benkhant/NorthStar-Adaptation-Guide/LinkedListAR_Unity6/Assets/Markers/head_20.png

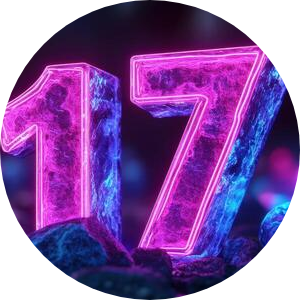
LinkedListAR_Unity6/Assets/Markers/head_20.png
