benkhant/NorthStar-Adaptation-Guide/LinkedListAR_Unity6/Assets/Markers/head_30.png

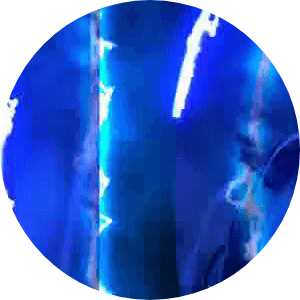
LinkedListAR_Unity6/Assets/Markers/head_30.png
