benkhant/NorthStar-Adaptation-Guide/LinkedListAR_Unity6/Assets/Markers/head_45.png

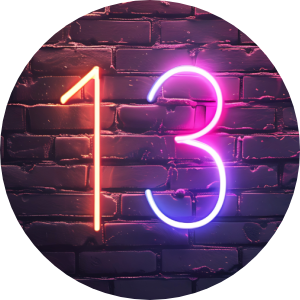
LinkedListAR_Unity6/Assets/Markers/head_45.png
