benkhant/NorthStar-Adaptation-Guide/LinkedListAR_Unity6/Assets/Markers/node_10.png

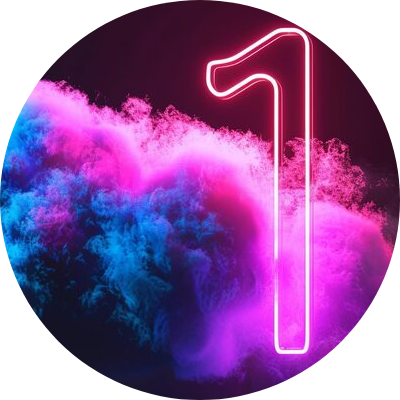
LinkedListAR_Unity6/Assets/Markers/node_10.png
