benkhant/NorthStar-Adaptation-Guide/LinkedListAR_Unity6/Assets/Markers/node_15.png

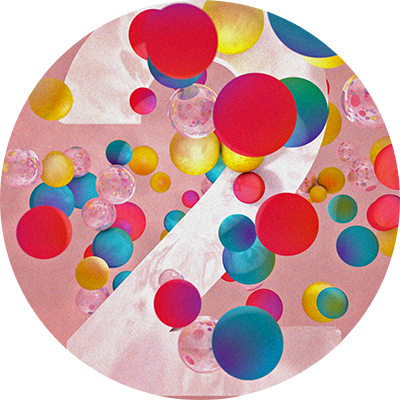
LinkedListAR_Unity6/Assets/Markers/node_15.png
