benkhant/NorthStar-Adaptation-Guide/LinkedListAR_Unity6/Assets/Markers/node_20.png

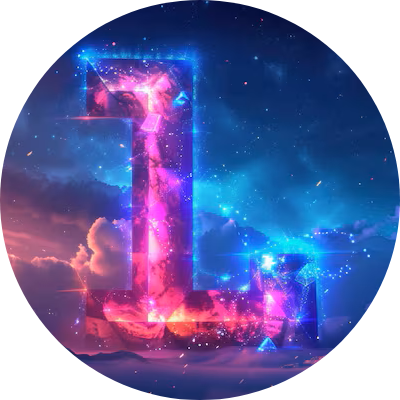
LinkedListAR_Unity6/Assets/Markers/node_20.png
