benkhant/NorthStar-Adaptation-Guide/LinkedListAR_Unity6/Assets/Markers/node_45.png

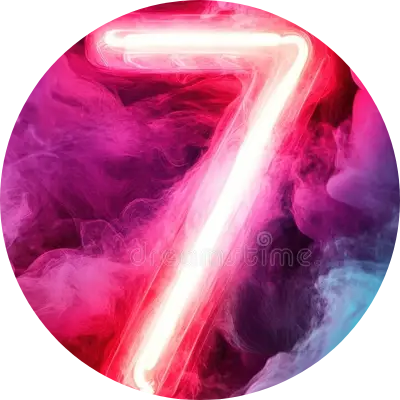
LinkedListAR_Unity6/Assets/Markers/node_45.png
