benkhant/NorthStar-Adaptation-Guide/LinkedListAR_Unity6/Assets/MRTK/Examples/Demos/EyeTracking/DemoScrollPanZoom/Textures/scrollbarhandle.png

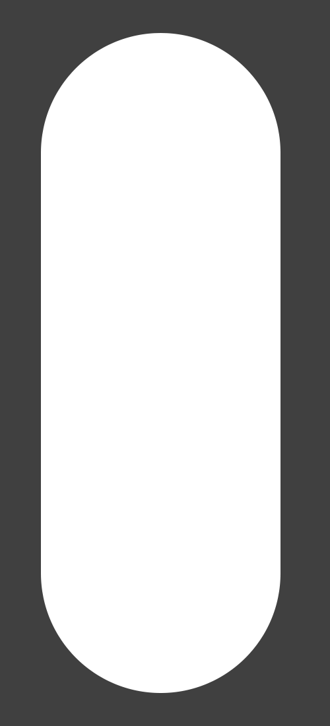
LinkedListAR_Unity6/Assets/MRTK/Examples/Demos/EyeTracking/DemoScrollPanZoom/Textures/scrollbarhandle.png
