benkhant/NorthStar-Adaptation-Guide/LinkedListAR_Unity6/Assets/MRTK/Examples/Demos/EyeTracking/DemoScrollPanZoom/Textures/tex_PanAndZoom_text.png

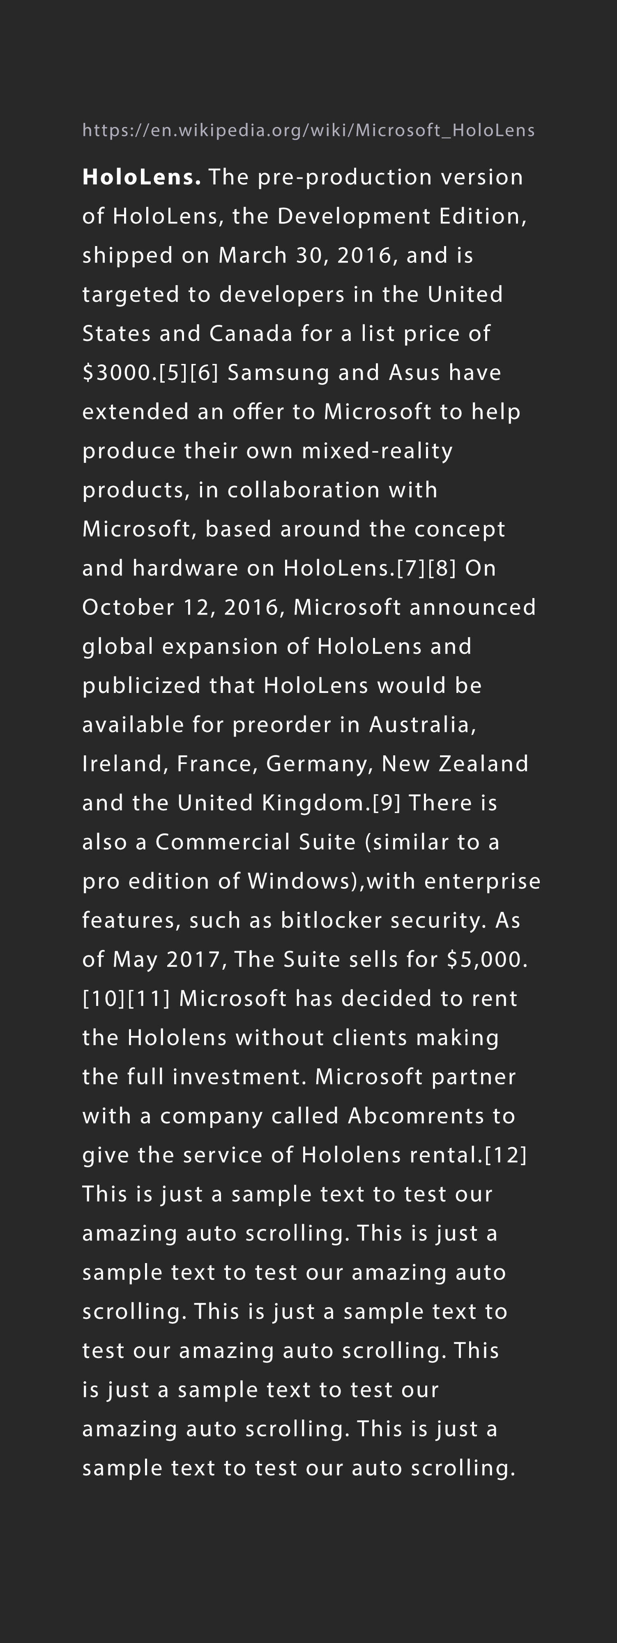
LinkedListAR_Unity6/Assets/MRTK/Examples/Demos/EyeTracking/DemoScrollPanZoom/Textures/tex_PanAndZoom_text.png
