benkhant/NorthStar-Adaptation-Guide/LinkedListAR_Unity6/Assets/MRTK/Examples/Demos/EyeTracking/DemoVisualizer/Textures/tex_picture2.jpg

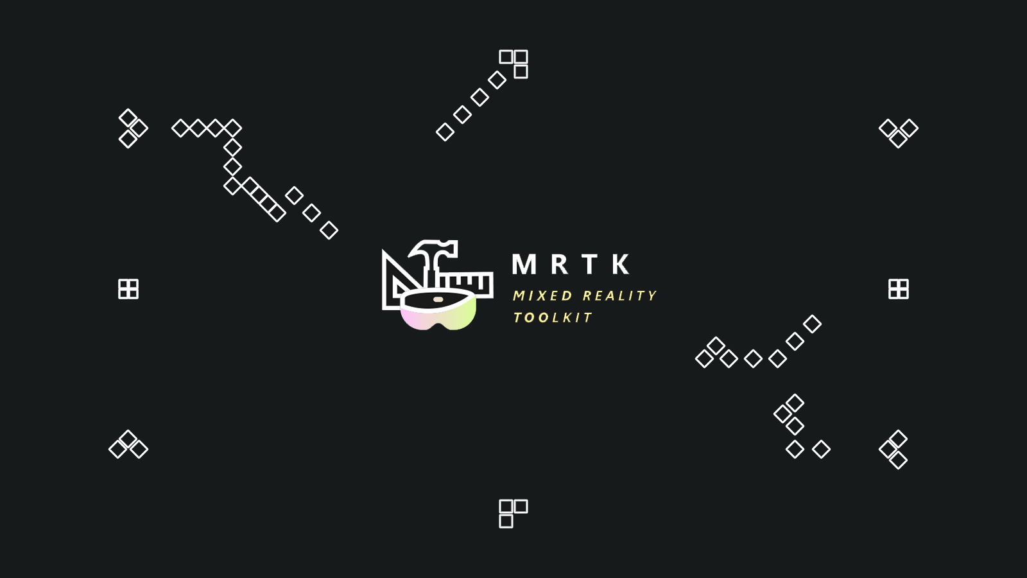
LinkedListAR_Unity6/Assets/MRTK/Examples/Demos/EyeTracking/DemoVisualizer/Textures/tex_picture2.jpg
