benkhant/NorthStar-Adaptation-Guide/LinkedListAR_Unity6/Assets/MRTK/Examples/Demos/EyeTracking/General/Textures/tex_blank_tile.png

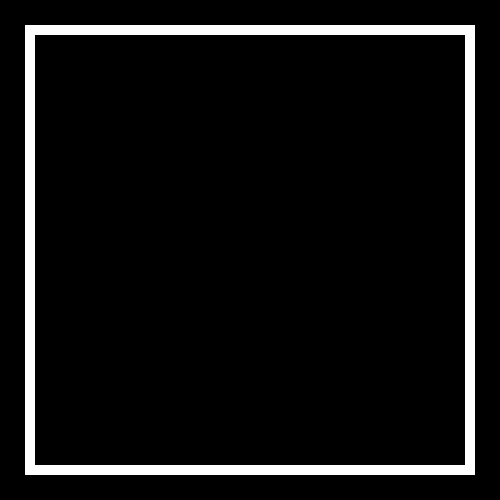
LinkedListAR_Unity6/Assets/MRTK/Examples/Demos/EyeTracking/General/Textures/tex_blank_tile.png
