benkhant/NorthStar-Adaptation-Guide/LinkedListAR_Unity6/Assets/MRTK/Examples/Demos/Gltf/Models/Avocado/glTF/Avocado_baseColor.png

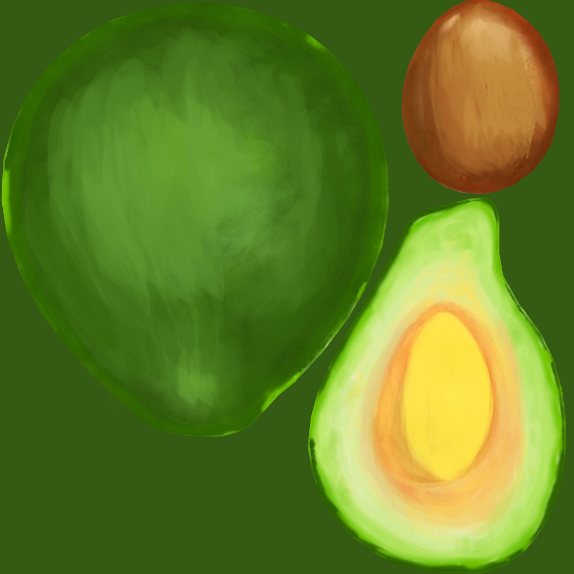
LinkedListAR_Unity6/Assets/MRTK/Examples/Demos/Gltf/Models/Avocado/glTF/Avocado_baseColor.png
