benkhant/NorthStar-Adaptation-Guide/LinkedListAR_Unity6/Assets/MRTK/Examples/Demos/UX/Interactables/Textures/PhysicalTouch.png

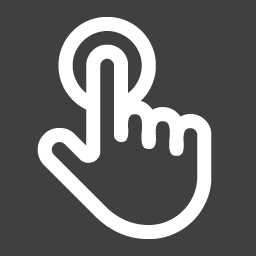
LinkedListAR_Unity6/Assets/MRTK/Examples/Demos/UX/Interactables/Textures/PhysicalTouch.png
