benkhant/NorthStar-Adaptation-Guide/LinkedListAR_Unity6/Assets/MRTK/Examples/StandardAssets/Models/CoffeeCup 1.fbm/5.png

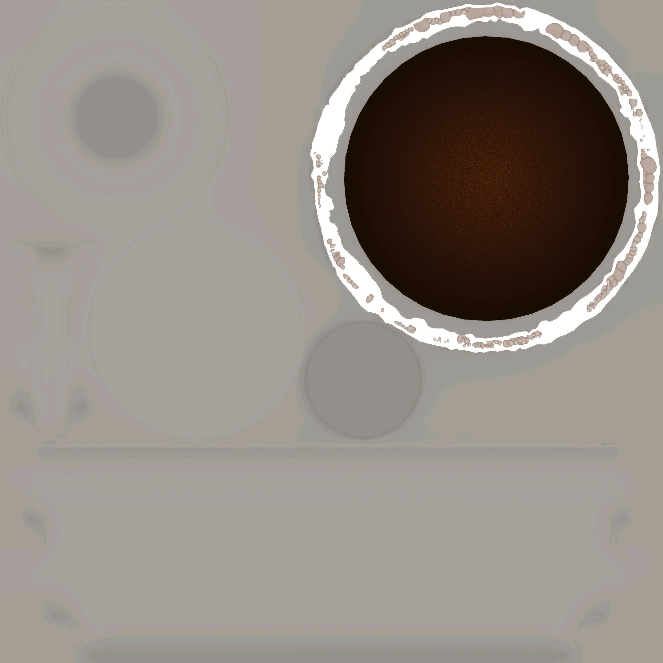
LinkedListAR_Unity6/Assets/MRTK/Examples/StandardAssets/Models/CoffeeCup 1.fbm/5.png
