benkhant/NorthStar-Adaptation-Guide/LinkedListAR_Unity6/Assets/MRTK/Examples/StandardAssets/Models/EarthCore.fbm/7.png

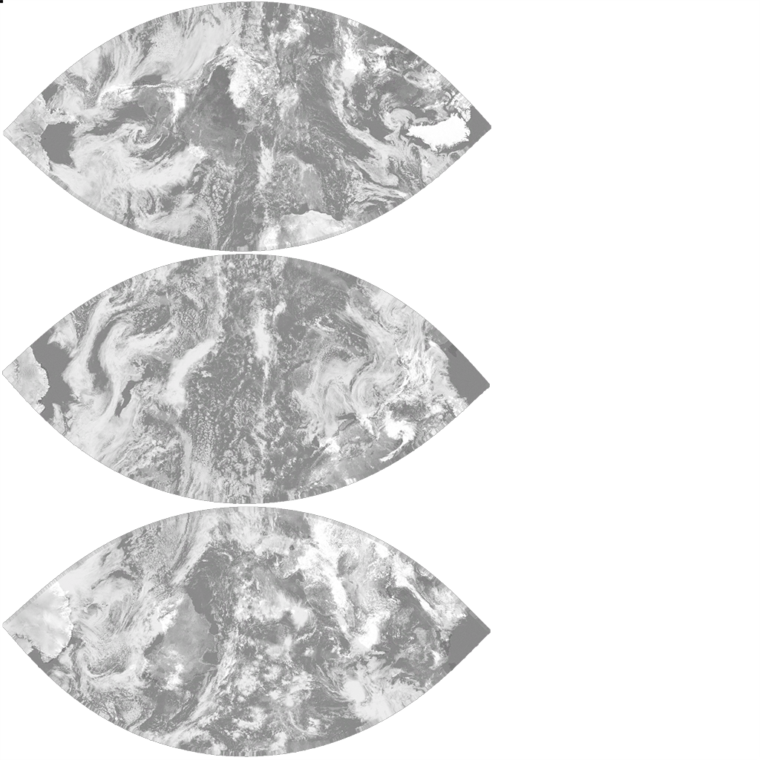
LinkedListAR_Unity6/Assets/MRTK/Examples/StandardAssets/Models/EarthCore.fbm/7.png
