benkhant/NorthStar-Adaptation-Guide/LinkedListAR_Unity6/Assets/MRTK/Examples/StandardAssets/Models/MarsCuriosityRover.fbm/6.png

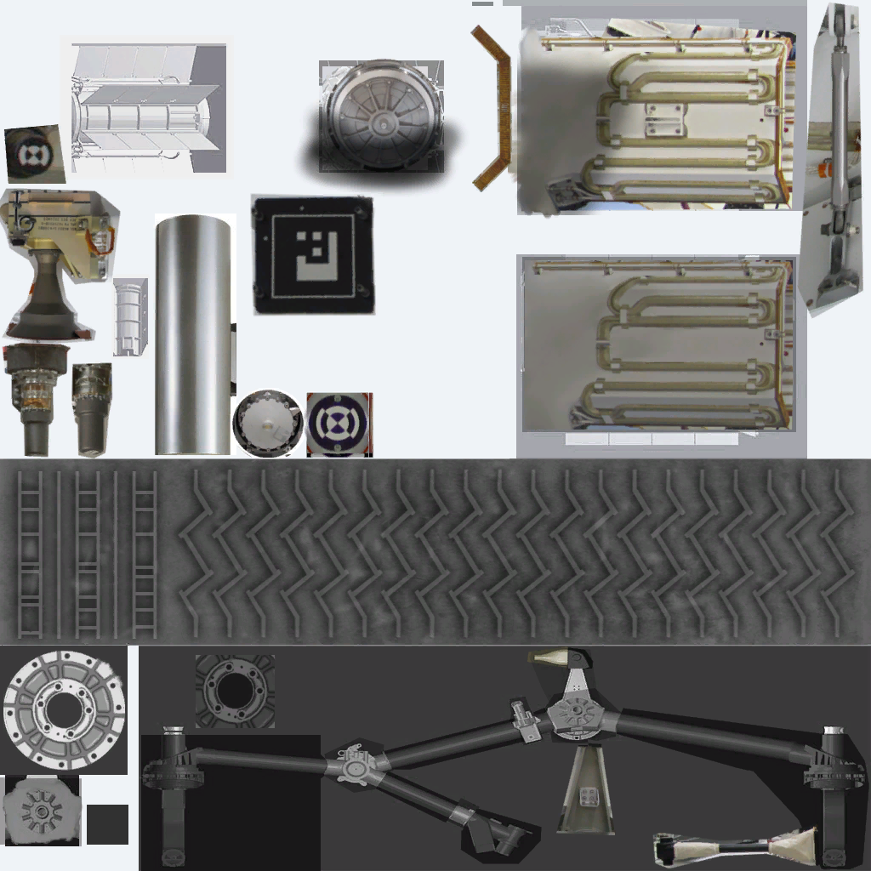
LinkedListAR_Unity6/Assets/MRTK/Examples/StandardAssets/Models/MarsCuriosityRover.fbm/6.png
