benkhant/NorthStar-Adaptation-Guide/LinkedListAR_Unity6/Assets/MRTK/Examples/StandardAssets/Models/MarsCuriosityRover.fbm/9.png

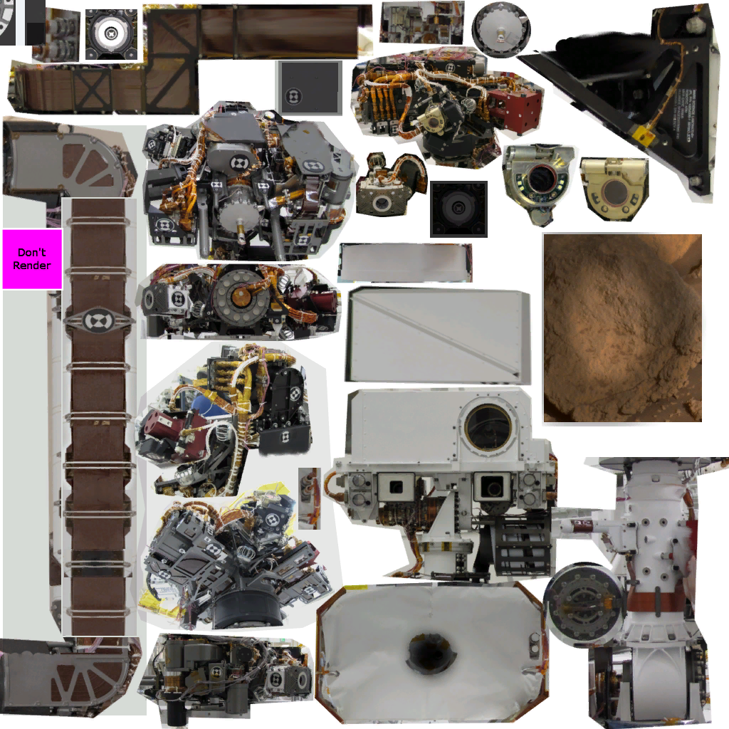
LinkedListAR_Unity6/Assets/MRTK/Examples/StandardAssets/Models/MarsCuriosityRover.fbm/9.png
