benkhant/NorthStar-Adaptation-Guide/LinkedListAR_Unity6/Assets/MRTK/Examples/StandardAssets/Textures/CoffeeFoam.png

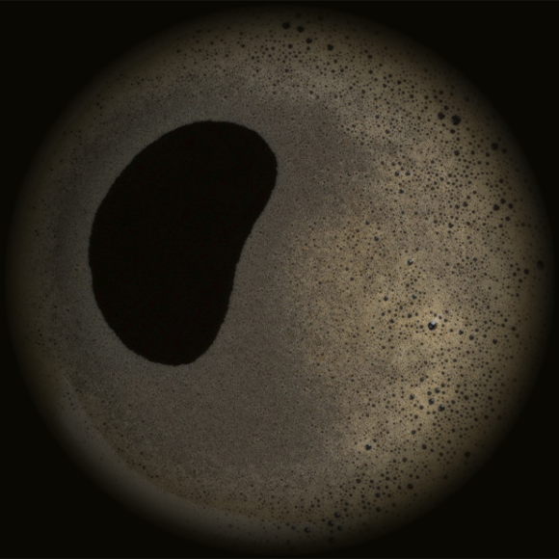
LinkedListAR_Unity6/Assets/MRTK/Examples/StandardAssets/Textures/CoffeeFoam.png
