benkhant/NorthStar-Adaptation-Guide/LinkedListAR_Unity6/Assets/MRTK/Examples/StandardAssets/Textures/Fabric_normal.png

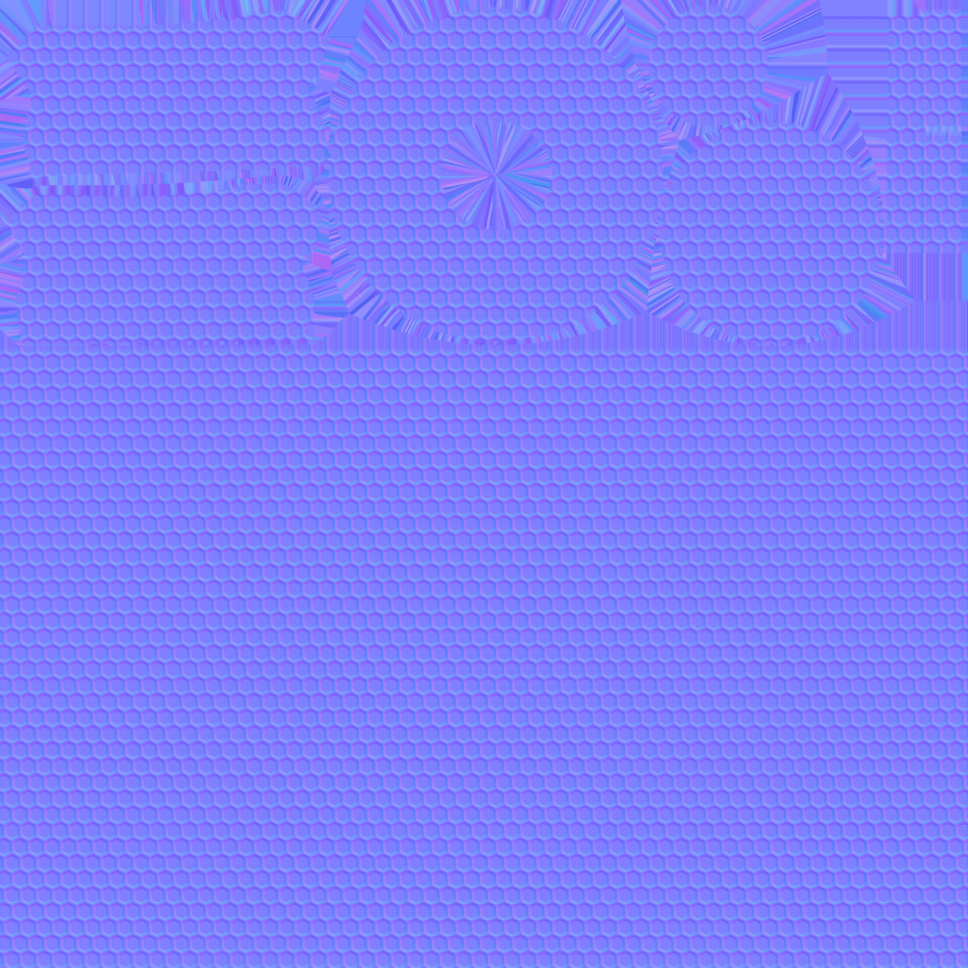
LinkedListAR_Unity6/Assets/MRTK/Examples/StandardAssets/Textures/Fabric_normal.png
