benkhant/NorthStar-Adaptation-Guide/LinkedListAR_Unity6/Assets/MRTK/Examples/StandardAssets/Textures/HumanHeart_Albdeo.png

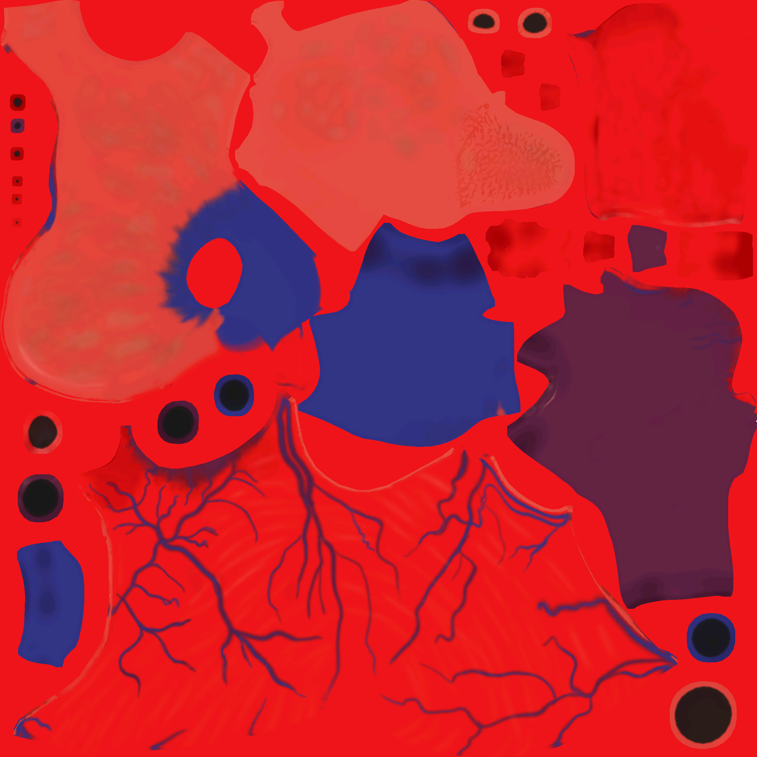
LinkedListAR_Unity6/Assets/MRTK/Examples/StandardAssets/Textures/HumanHeart_Albdeo.png
