benkhant/NorthStar-Adaptation-Guide/LinkedListAR_Unity6/Assets/MRTK/Examples/StandardAssets/Textures/PianoKeys_DIF.png

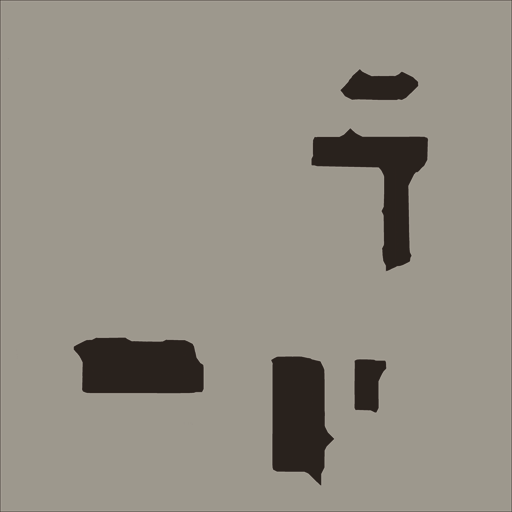
LinkedListAR_Unity6/Assets/MRTK/Examples/StandardAssets/Textures/PianoKeys_DIF.png
