benkhant/NorthStar-Adaptation-Guide/LinkedListAR_Unity6/Assets/MRTK/Examples/StandardAssets/Textures/PianoKeys_NM.png

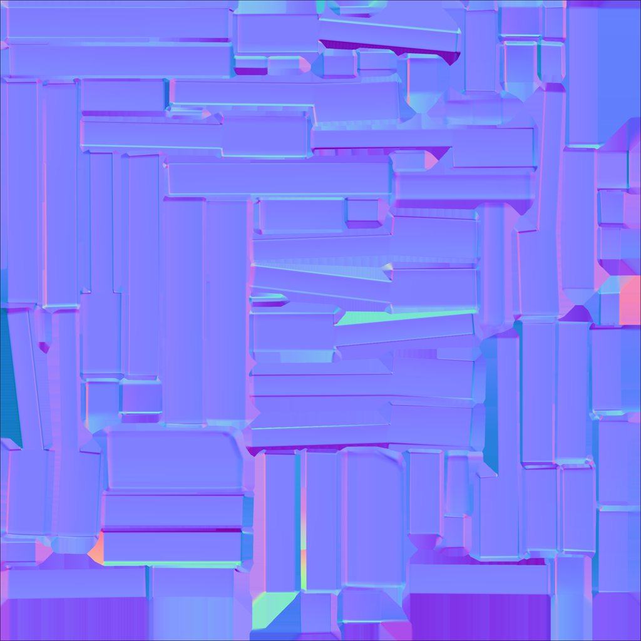
LinkedListAR_Unity6/Assets/MRTK/Examples/StandardAssets/Textures/PianoKeys_NM.png
