benkhant/NorthStar-Adaptation-Guide/LinkedListAR_Unity6/Assets/MRTK/Examples/StandardAssets/Textures/RustedIron_albedo.png

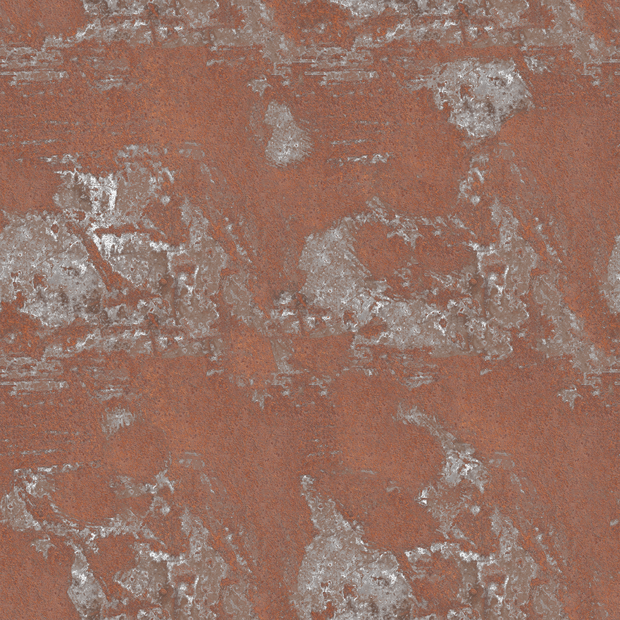
LinkedListAR_Unity6/Assets/MRTK/Examples/StandardAssets/Textures/RustedIron_albedo.png
