benkhant/NorthStar-Adaptation-Guide/LinkedListAR_Unity6/Assets/MRTK/Examples/StandardAssets/Textures/ShaderBall_albedo.png

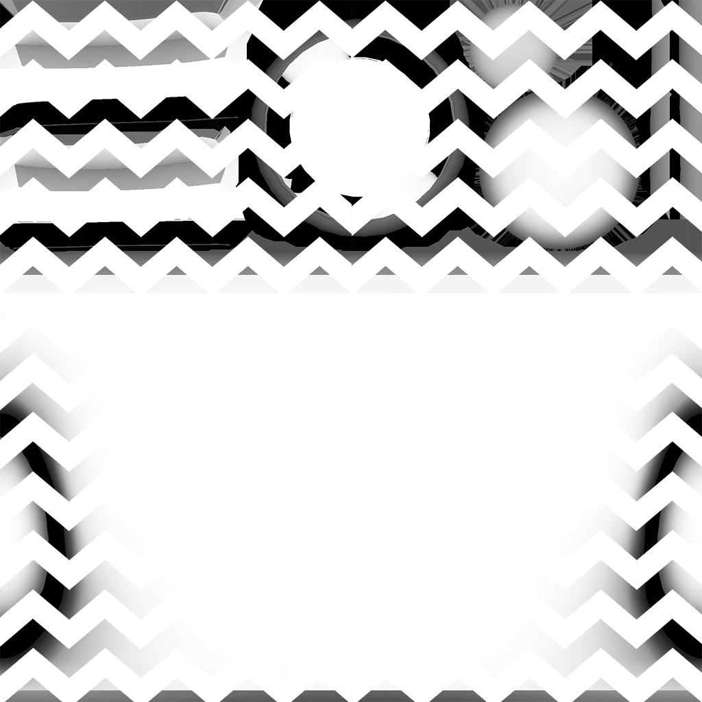
LinkedListAR_Unity6/Assets/MRTK/Examples/StandardAssets/Textures/ShaderBall_albedo.png
