benkhant/NorthStar-Adaptation-Guide/LinkedListAR_Unity6/Assets/MRTK/Examples/StandardAssets/Textures/ShaderBall_ao.png

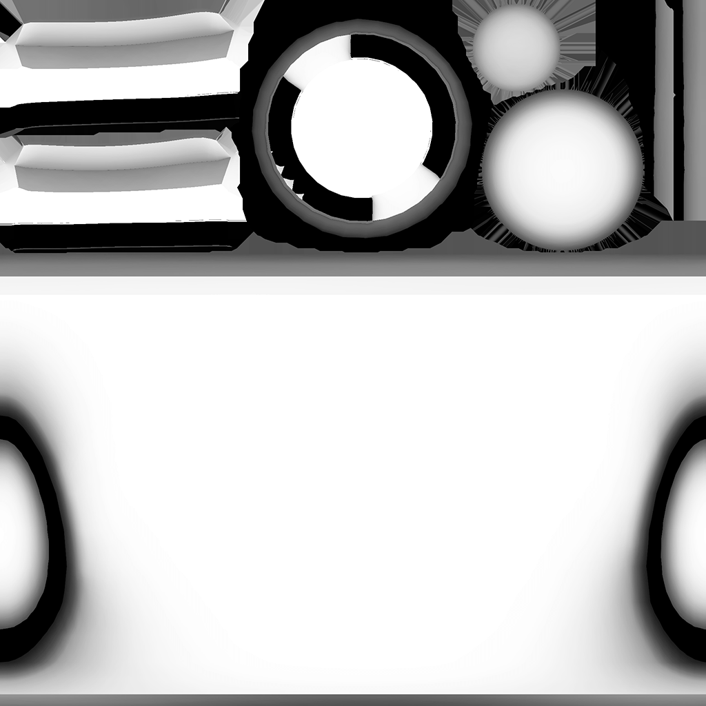
LinkedListAR_Unity6/Assets/MRTK/Examples/StandardAssets/Textures/ShaderBall_ao.png
