benkhant/NorthStar-Adaptation-Guide/LinkedListAR_Unity6/Assets/MRTK/Examples/StandardAssets/Textures/ShaderBallNoise_albedo.png

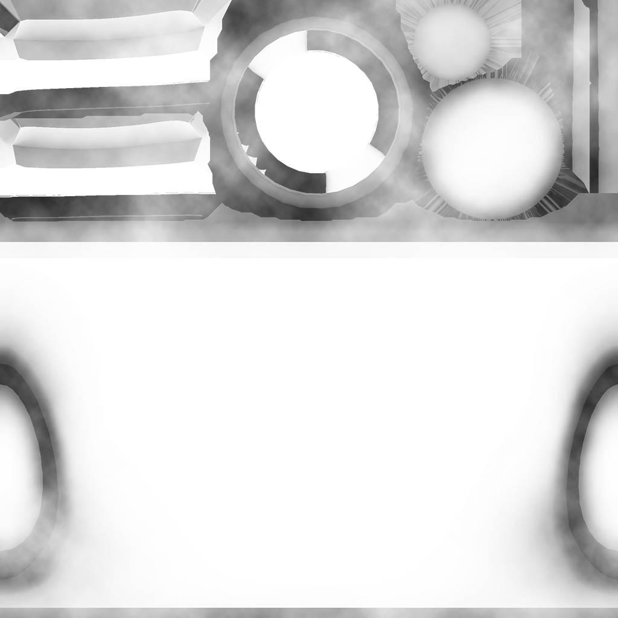
LinkedListAR_Unity6/Assets/MRTK/Examples/StandardAssets/Textures/ShaderBallNoise_albedo.png
