benkhant/NorthStar-Adaptation-Guide/LinkedListAR_Unity6/Assets/MRTK/Extensions/LostTrackingService/Assets/color_palette.png

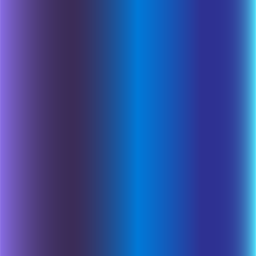
LinkedListAR_Unity6/Assets/MRTK/Extensions/LostTrackingService/Assets/color_palette.png
