benkhant/NorthStar-Adaptation-Guide/LinkedListAR_Unity6/Assets/MRTK/SDK/StandardAssets/Textures/Checker_albedo.png

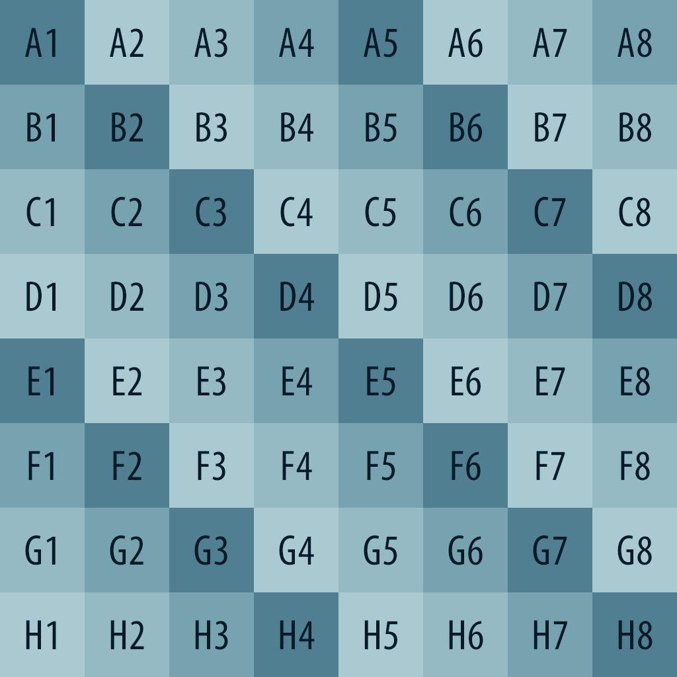
LinkedListAR_Unity6/Assets/MRTK/SDK/StandardAssets/Textures/Checker_albedo.png
