benkhant/NorthStar-Adaptation-Guide/LinkedListAR_Unity6/Assets/MRTK/SDK/StandardAssets/Textures/Circle.png

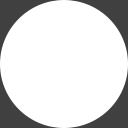
LinkedListAR_Unity6/Assets/MRTK/SDK/StandardAssets/Textures/Circle.png
