benkhant/NorthStar-Adaptation-Guide/LinkedListAR_Unity6/Assets/MRTK/SDK/StandardAssets/Textures/GrabArea.png

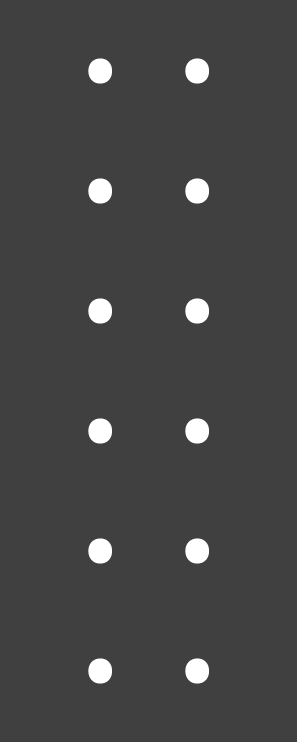
LinkedListAR_Unity6/Assets/MRTK/SDK/StandardAssets/Textures/GrabArea.png
