benkhant/NorthStar-Adaptation-Guide/LinkedListAR_Unity6/Assets/MRTK/SDK/StandardAssets/Textures/PanExampleContent.jpg

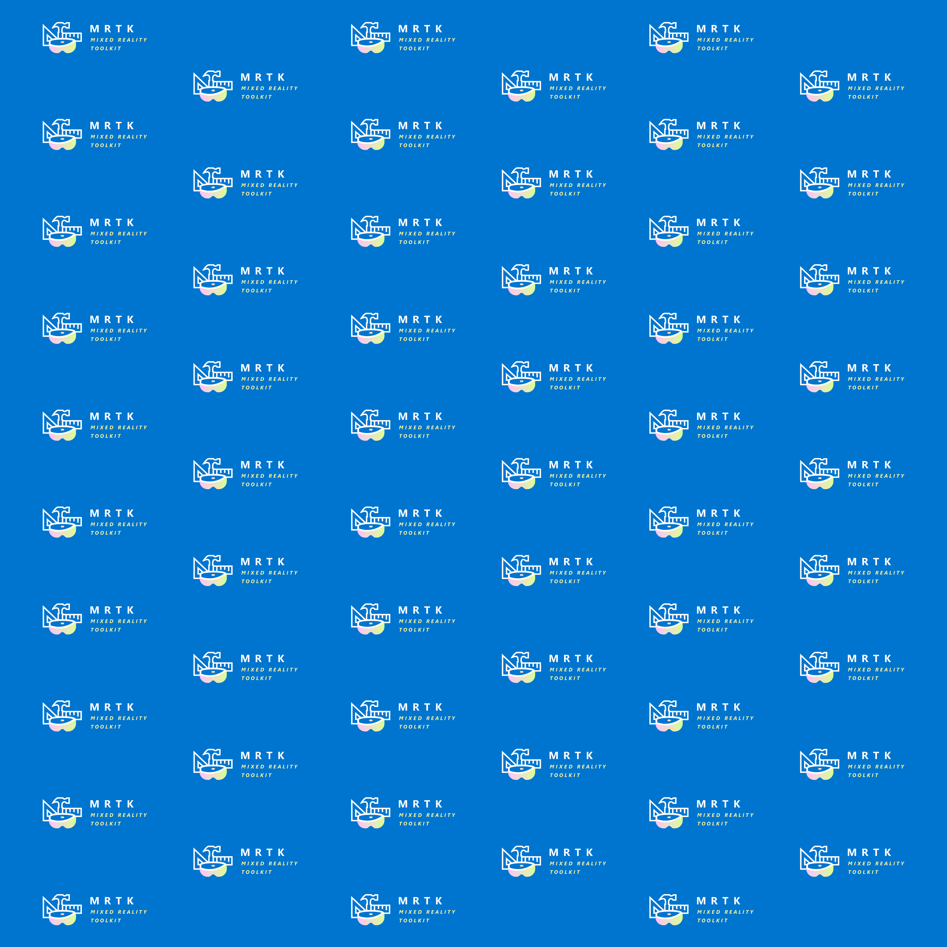
LinkedListAR_Unity6/Assets/MRTK/SDK/StandardAssets/Textures/PanExampleContent.jpg
