benkhant/NorthStar-Adaptation-Guide/LinkedListAR_Unity6/Assets/MRTK/SDK/StandardAssets/Textures/ResetRotation.png

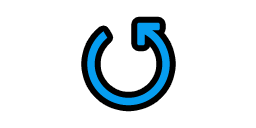
LinkedListAR_Unity6/Assets/MRTK/SDK/StandardAssets/Textures/ResetRotation.png
