benkhant/NorthStar-Adaptation-Guide/LinkedListAR_Unity6/Assets/MRTK/StandardAssets/Textures/Generic_controller_black_scaled.png

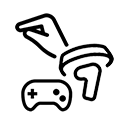
LinkedListAR_Unity6/Assets/MRTK/StandardAssets/Textures/Generic_controller_black_scaled.png
