benkhant/NorthStar-Adaptation-Guide/LinkedListAR_Unity6/Assets/MRTK/StandardAssets/Textures/Generic_controller_white_scaled.png

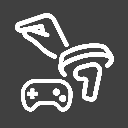
LinkedListAR_Unity6/Assets/MRTK/StandardAssets/Textures/Generic_controller_white_scaled.png
