benkhant/NorthStar-Adaptation-Guide/LinkedListAR_Unity6/Assets/MRTK/StandardAssets/Textures/IridescentSpectrum.png

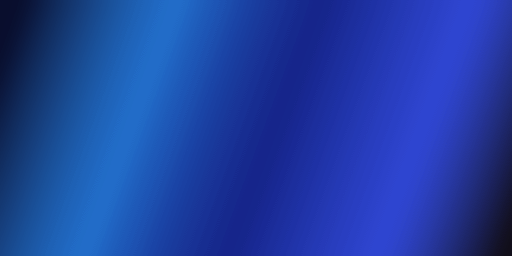
LinkedListAR_Unity6/Assets/MRTK/StandardAssets/Textures/IridescentSpectrum.png
