benkhant/NorthStar-Adaptation-Guide/LinkedListAR_Unity6/Assets/MRTK/StandardAssets/Textures/MotionController_left_black.png

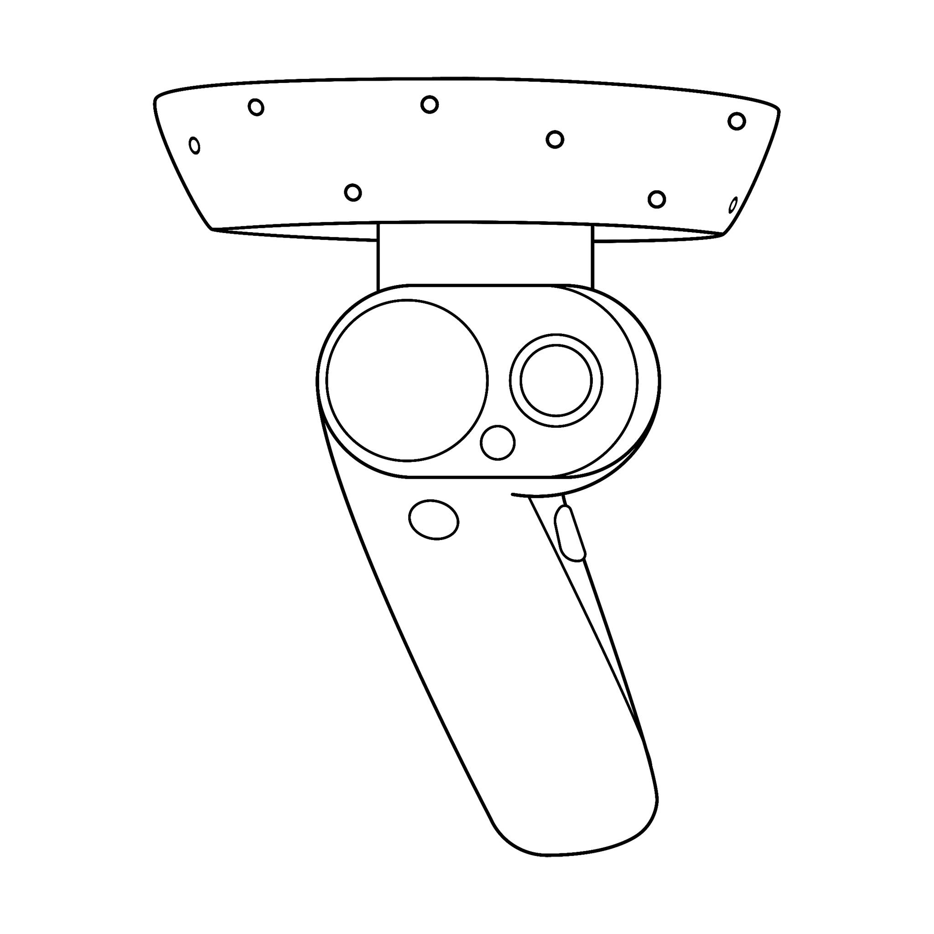
LinkedListAR_Unity6/Assets/MRTK/StandardAssets/Textures/MotionController_left_black.png
