benkhant/NorthStar-Adaptation-Guide/LinkedListAR_Unity6/Assets/MRTK/StandardAssets/Textures/OculusControllersTouch_left_white.png

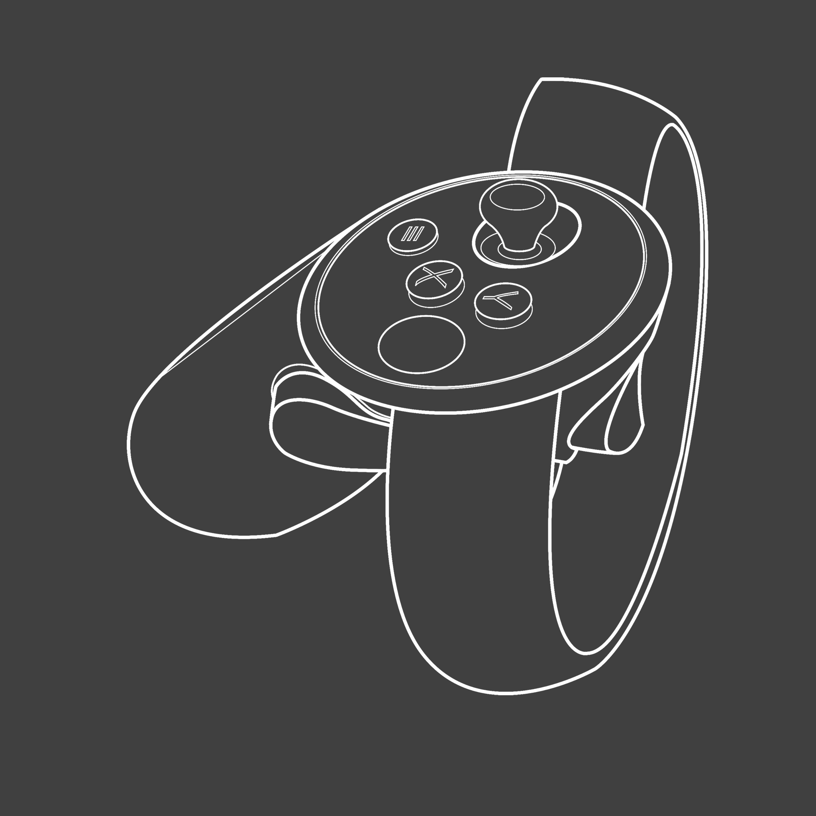
LinkedListAR_Unity6/Assets/MRTK/StandardAssets/Textures/OculusControllersTouch_left_white.png
