benkhant/NorthStar-Adaptation-Guide/LinkedListAR_Unity6/Assets/MRTK/StandardAssets/Textures/OculusControllersTouch_right_white.png

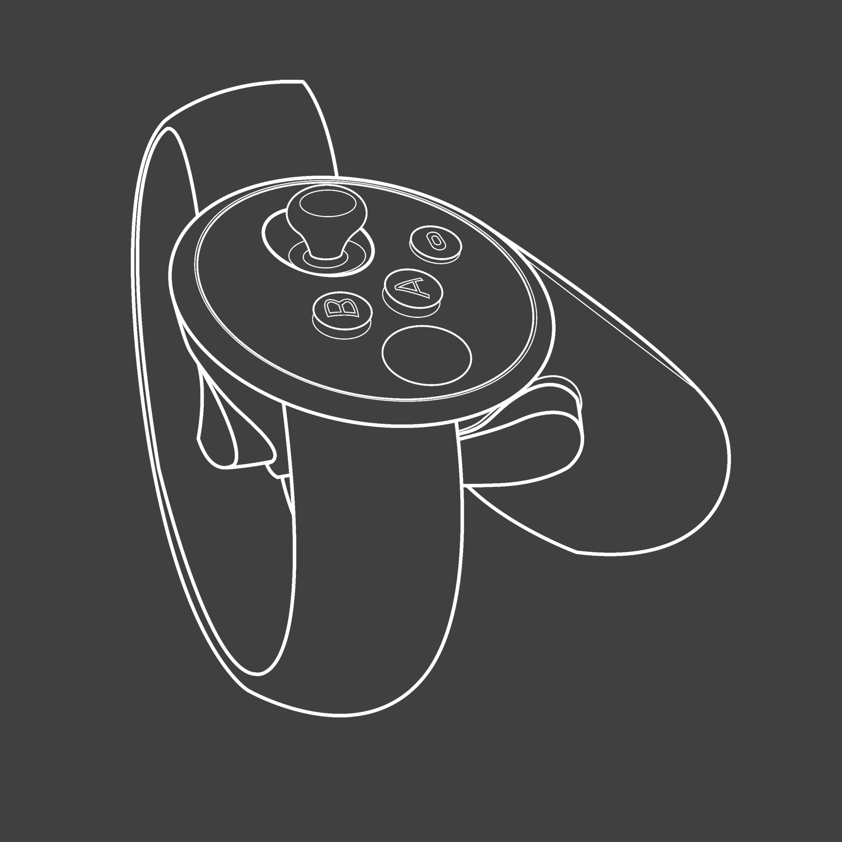
LinkedListAR_Unity6/Assets/MRTK/StandardAssets/Textures/OculusControllersTouch_right_white.png
