benkhant/NorthStar-Adaptation-Guide/LinkedListAR_Unity6/Assets/MRTK/StandardAssets/Textures/OculusRemoteController_black.png

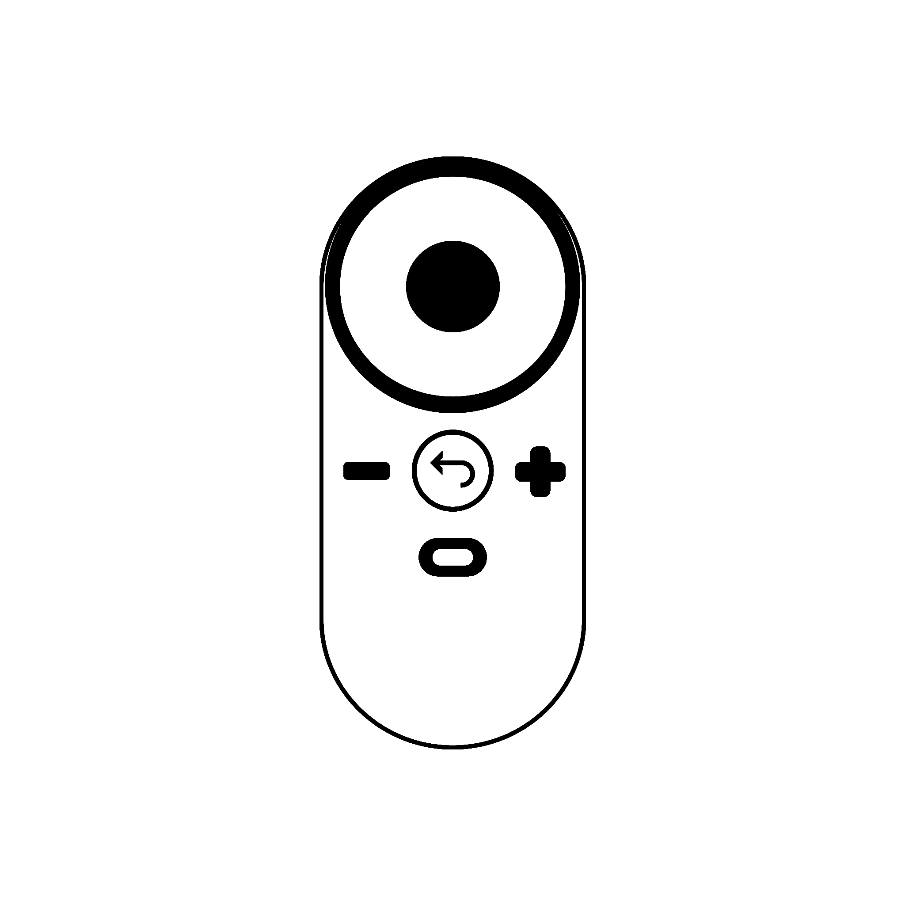
LinkedListAR_Unity6/Assets/MRTK/StandardAssets/Textures/OculusRemoteController_black.png
