benkhant/NorthStar-Adaptation-Guide/LinkedListAR_Unity6/Assets/MRTK/StandardAssets/Textures/OculusRemoteController_white.png

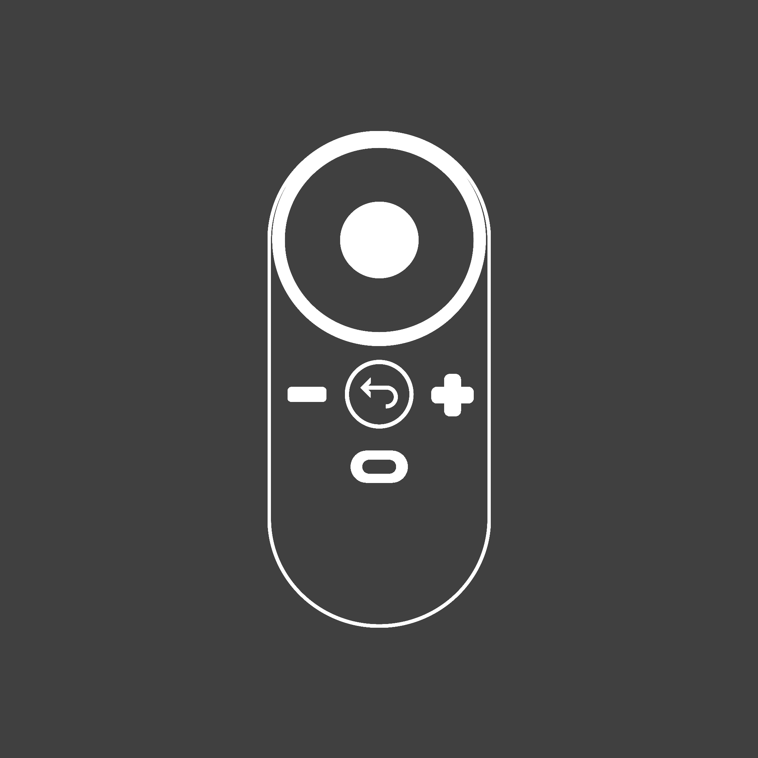
LinkedListAR_Unity6/Assets/MRTK/StandardAssets/Textures/OculusRemoteController_white.png
