benkhant/NorthStar-Adaptation-Guide/LinkedListAR_Unity6/Assets/Plugins/LeapMotion/Core/EditorResources/HandTex.png

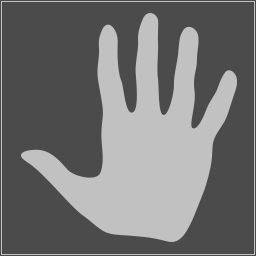
LinkedListAR_Unity6/Assets/Plugins/LeapMotion/Core/EditorResources/HandTex.png
