benkhant/NorthStar-Adaptation-Guide/LinkedListAR_Unity6/Assets/Plugins/LeapMotion/Core/Textures/LoPolyHand_Color.png

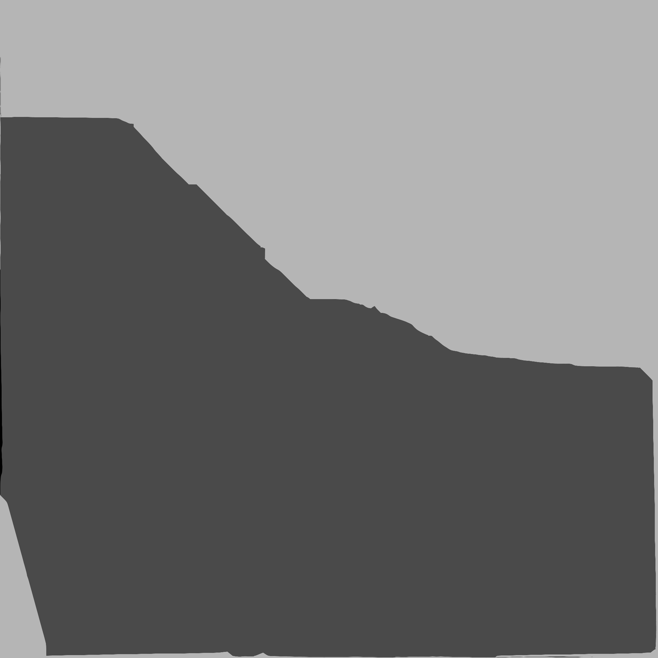
LinkedListAR_Unity6/Assets/Plugins/LeapMotion/Core/Textures/LoPolyHand_Color.png
