benkhant/NorthStar-Adaptation-Guide/LinkedListAR_Unity6/Assets/Plugins/LeapMotion/Core/Textures/PluginLeapNotice.png

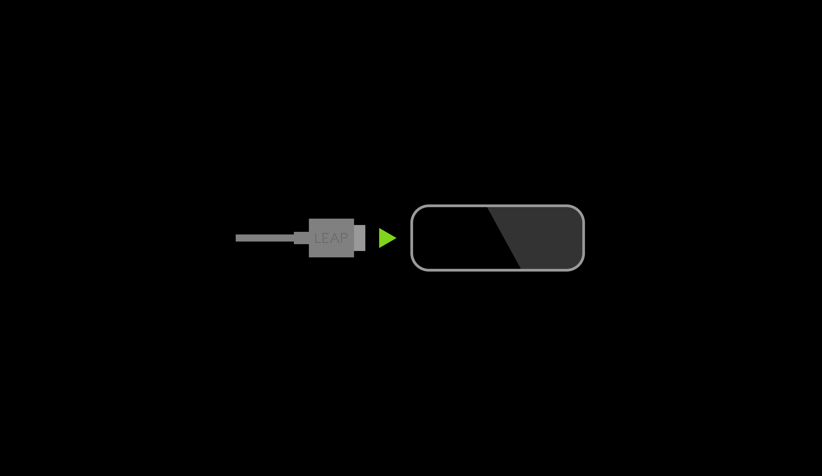
LinkedListAR_Unity6/Assets/Plugins/LeapMotion/Core/Textures/PluginLeapNotice.png
