benkhant/NorthStar-Adaptation-Guide/LinkedListAR_Unity6/Assets/Plugins/LeapMotion/Core/Textures/PluginLeapNoticeLarge.png

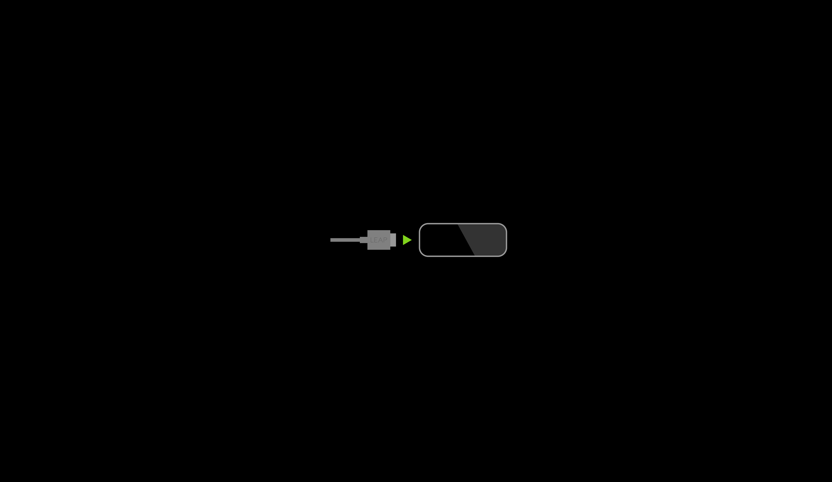
LinkedListAR_Unity6/Assets/Plugins/LeapMotion/Core/Textures/PluginLeapNoticeLarge.png
