benkhant/NorthStar-Adaptation-Guide/LinkedListAR_Unity6/Assets/Resources/Gesture/e11.png

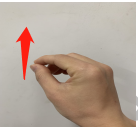
LinkedListAR_Unity6/Assets/Resources/Gesture/e11.png
