benkhant/NorthStar-Adaptation-Guide/LinkedListAR_Unity6/Assets/Resources/Gesture/e12.png

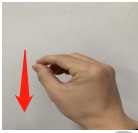
LinkedListAR_Unity6/Assets/Resources/Gesture/e12.png
