benkhant/NorthStar-Adaptation-Guide/LinkedListAR_Unity6/Assets/Resources/Gesture/e13.png

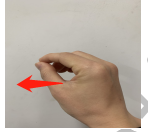
LinkedListAR_Unity6/Assets/Resources/Gesture/e13.png
