benkhant/NorthStar-Adaptation-Guide/LinkedListAR_Unity6/Assets/Resources/Gesture/e14.png

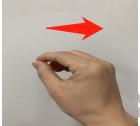
LinkedListAR_Unity6/Assets/Resources/Gesture/e14.png
