benkhant/NorthStar-Adaptation-Guide/LinkedListAR_Unity6/Assets/Resources/Gesture/g02.png

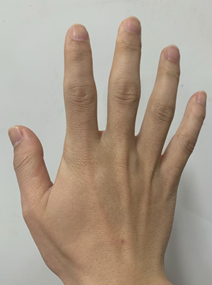
LinkedListAR_Unity6/Assets/Resources/Gesture/g02.png
