benkhant/NorthStar-Adaptation-Guide/LinkedListAR_Unity6/Assets/Resources/Gesture/g05.png

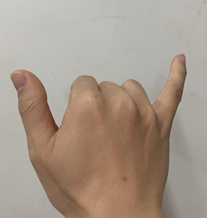
LinkedListAR_Unity6/Assets/Resources/Gesture/g05.png
