benkhant/NorthStar-Adaptation-Guide/LinkedListAR_Unity6/Assets/Resources/Gesture/g06.png

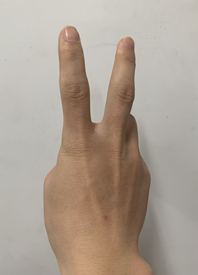
LinkedListAR_Unity6/Assets/Resources/Gesture/g06.png
