benkhant/NorthStar-Adaptation-Guide/LinkedListAR_Unity6/Assets/Resources/Gesture/g08.png

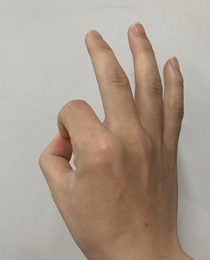
LinkedListAR_Unity6/Assets/Resources/Gesture/g08.png
