benkhant/NorthStar-Adaptation-Guide/LinkedListAR_Unity6/Assets/Resources/Gesture/g70.png

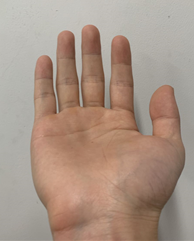
LinkedListAR_Unity6/Assets/Resources/Gesture/g70.png
