benkhant/NorthStar-Adaptation-Guide/LinkedListAR_Unity6/Assets/Settings/Project Configuration/TemplateImage.png

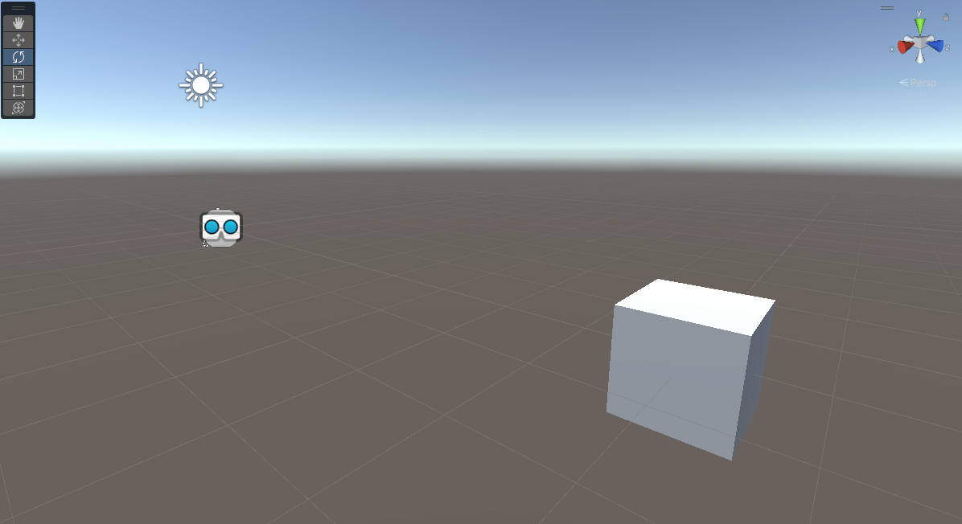
LinkedListAR_Unity6/Assets/Settings/Project Configuration/TemplateImage.png
