benkhant/NorthStar-Adaptation-Guide/software/Assets/UnityXRContent/Common/ReferenceImages/Rafflesia.jpg

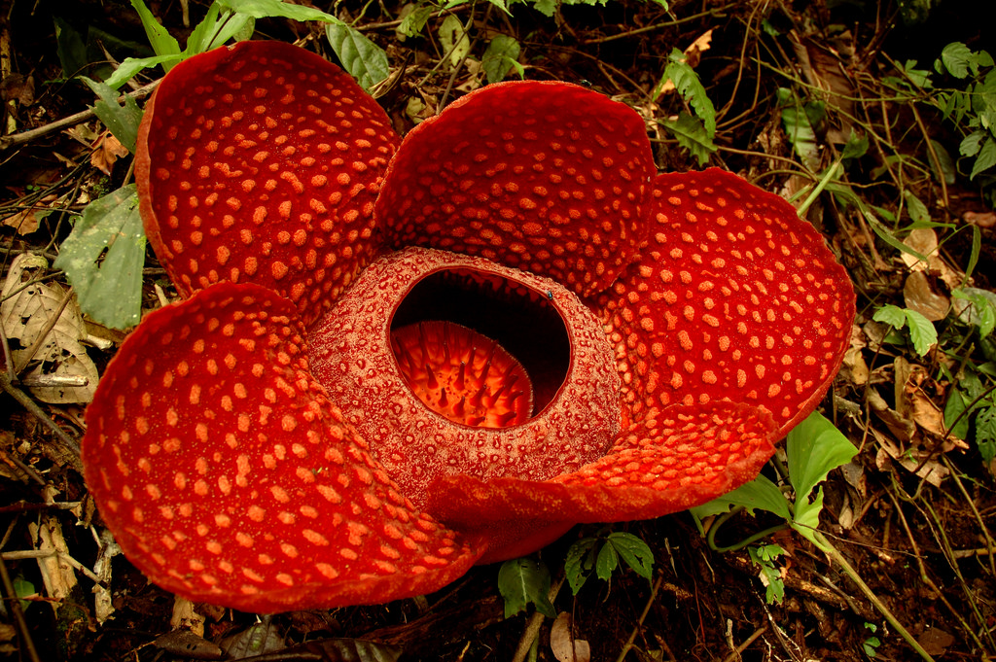
software/Assets/UnityXRContent/Common/ReferenceImages/Rafflesia.jpg
