benkhant/NorthStar-Adaptation-Guide/LinkedListAR_Unity6/Assets/MRTK/Examples/Experimental/Elastic/Materials/springs.png

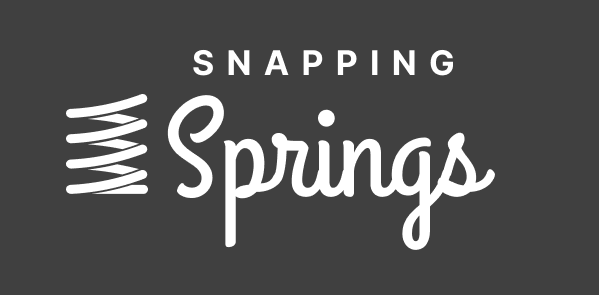
LinkedListAR_Unity6/Assets/MRTK/Examples/Experimental/Elastic/Materials/springs.png
