benkhant/NorthStar-Adaptation-Guide/LinkedListAR_Unity6/Assets/MobileARTemplateAssets/Tutorial/Images/ARMobileTemplateImage.png

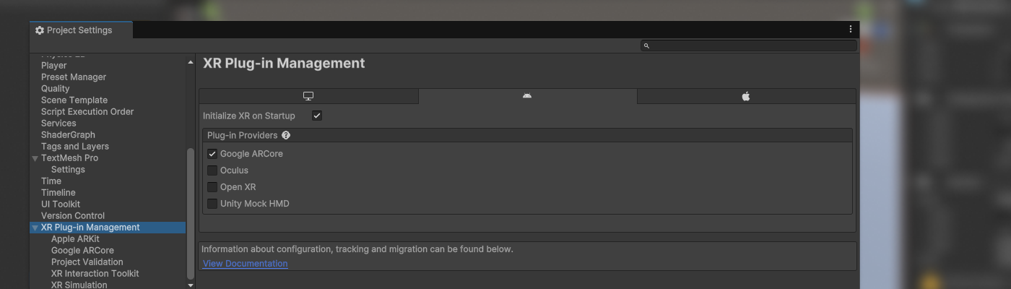
LinkedListAR_Unity6/Assets/MobileARTemplateAssets/Tutorial/Images/ARMobileTemplateImage.png
