benkhant/NorthStar-Adaptation-Guide/LinkedListAR_Unity6/Assets/MobileARTemplateAssets/Tutorial/Images/ARMobileThumbnailLarge.png

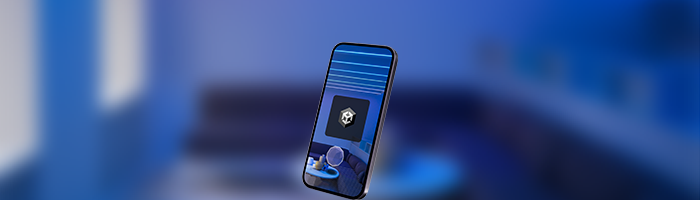
LinkedListAR_Unity6/Assets/MobileARTemplateAssets/Tutorial/Images/ARMobileThumbnailLarge.png
