benkhant/NorthStar-Adaptation-Guide/LinkedListAR_Unity6/Assets/MRTK/Examples/Experimental/ColorPicker/Textures/Dragger.png

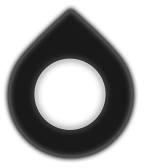
LinkedListAR_Unity6/Assets/MRTK/Examples/Experimental/ColorPicker/Textures/Dragger.png
