benkhant/NorthStar-Adaptation-Guide/LinkedListAR_Unity6/Assets/Plugins/LeapMotion/North Star/Scenes/Calibration/noise2[1].png

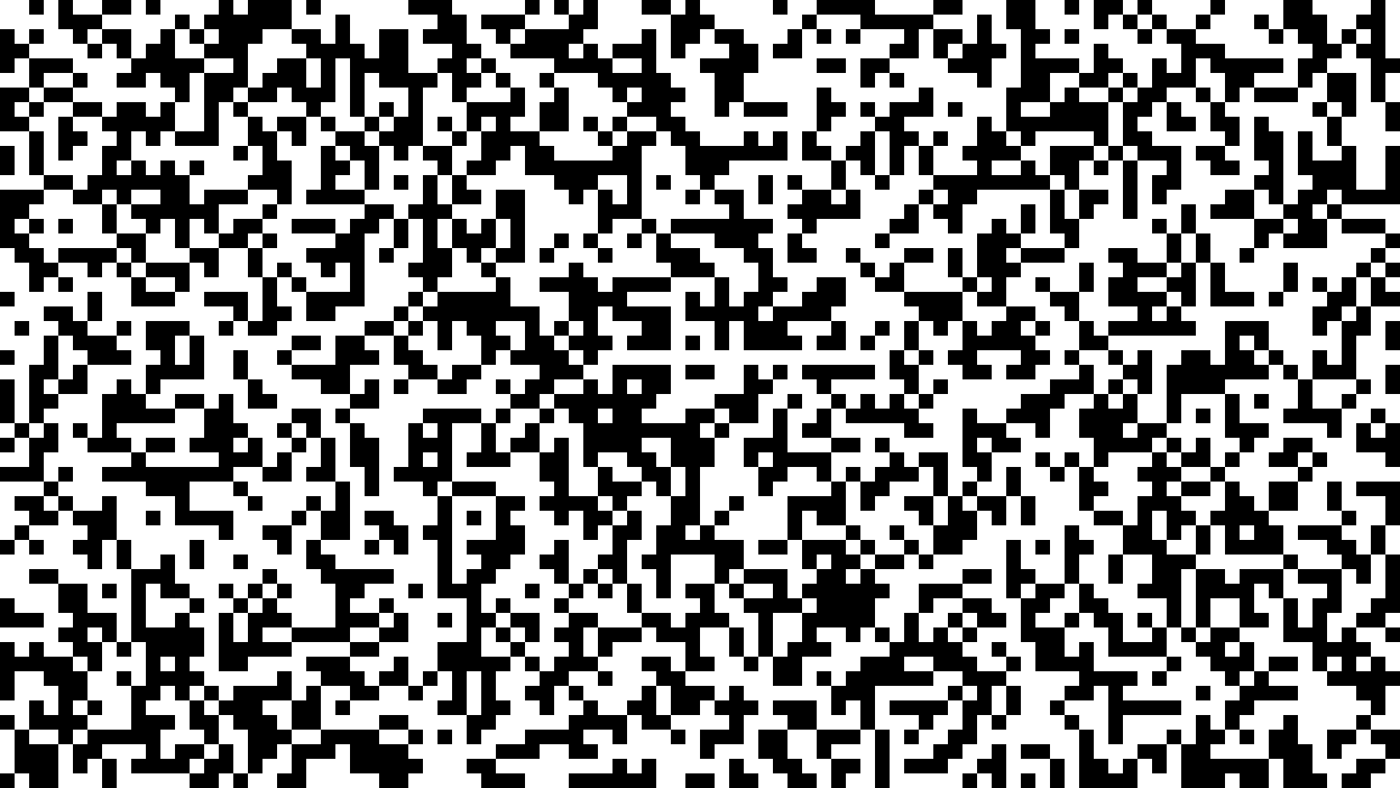
LinkedListAR_Unity6/Assets/Plugins/LeapMotion/North Star/Scenes/Calibration/noise2[1].png
