benkhant/NorthStar-Adaptation-Guide/LinkedListAR_Unity6/Assets/Plugins/LeapMotion/North Star/Scenes/Calibration/noise3_45deg-centerWhite.png

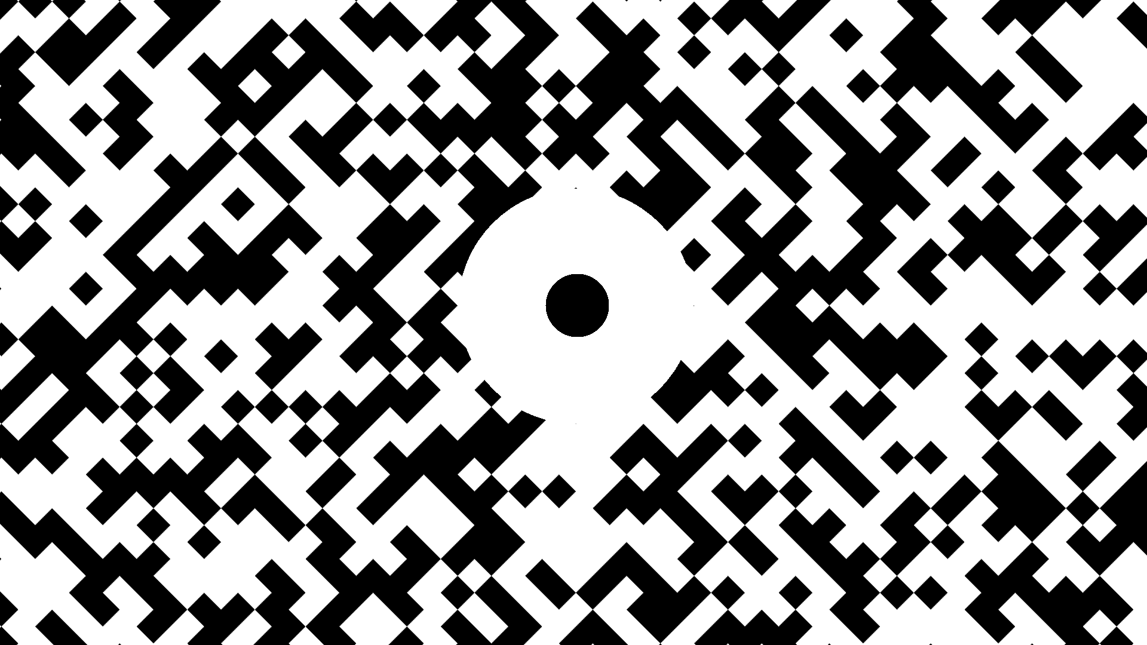
LinkedListAR_Unity6/Assets/Plugins/LeapMotion/North Star/Scenes/Calibration/noise3_45deg-centerWhite.png
