benkhant/NorthStar-Adaptation-Guide/LinkedListAR_Unity6/Assets/Plugins/LeapMotion/North Star/Scenes/Calibration/Spiral.png

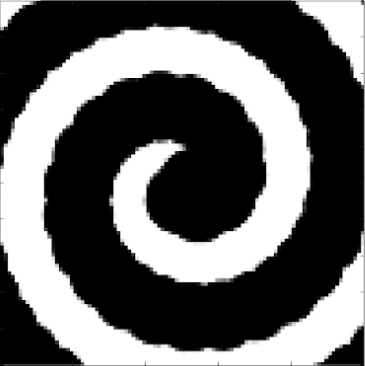
LinkedListAR_Unity6/Assets/Plugins/LeapMotion/North Star/Scenes/Calibration/Spiral.png
