benkhant/NorthStar-Adaptation-Guide/LinkedListAR_Unity6/Assets/Plugins/LeapMotion/North Star/Scenes/Calibration/test11.png

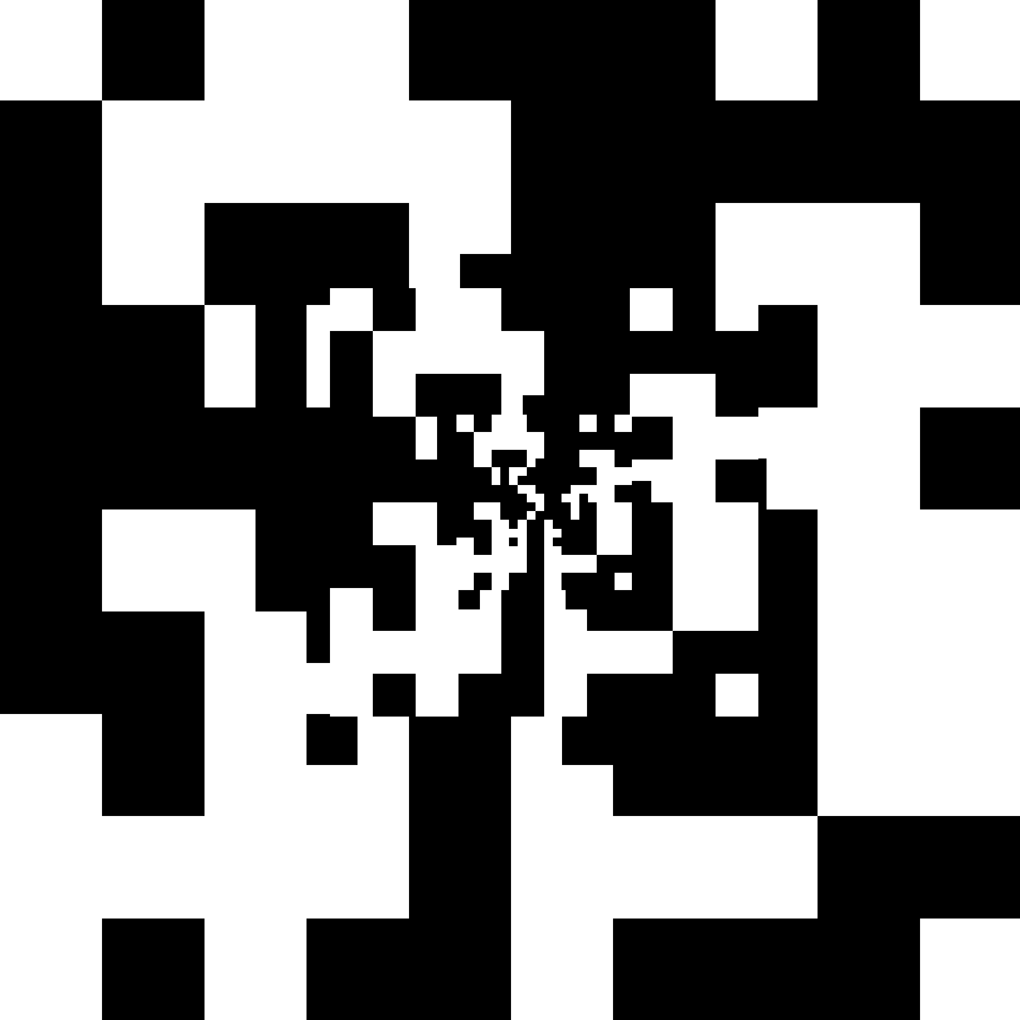
LinkedListAR_Unity6/Assets/Plugins/LeapMotion/North Star/Scenes/Calibration/test11.png
